adnbr/OpenBot/code/openbot-ntp-ssl/keys_example.h

// Complete the appropriate fields below and save as "keys.h"

#define api_host "api.thingspeak.com"
#define api_port 443
#define api_cert_hash "78 60 18 44 81 35 bf df 77 84 d4 0a 22 0d 9b 4e 6c dc 57 2c"
#define api_key ""
#define api_uri "/update"
#define api_twitter_feed ""

const char * ssid = "...";
const char * pass = "...";
